Daniel-Chin/A-V-H-General-Music-Tutoring-2022/hardware/3d_models/L4.stl

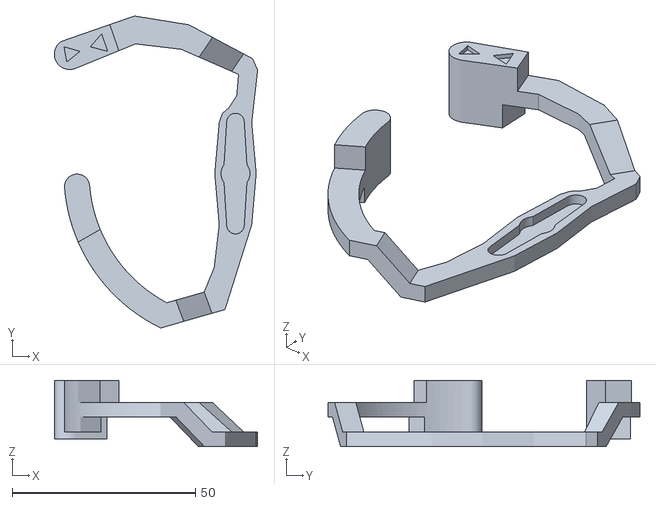
[picture p15: CAD file, 2022-03-28]
hardware/3d_models/L4.stl
55.4 x 85.1 x 18.0
